DiogoGoto/IAQ-Sensor/Data_Logging/Graphs/CO2.png

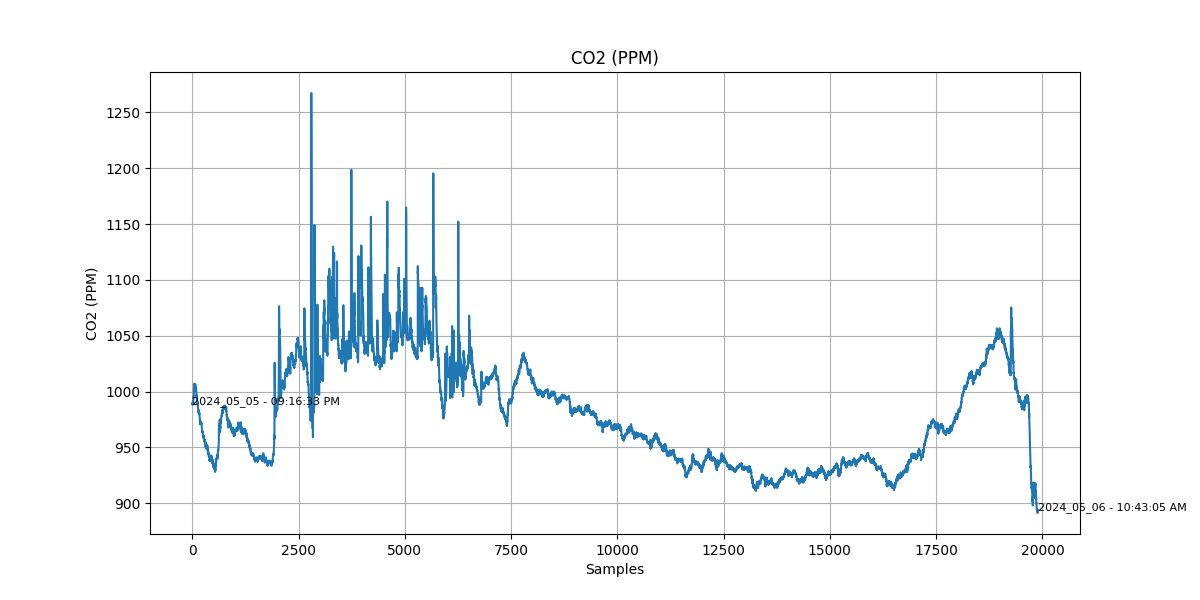
Data_Logging/Graphs/CO2.png
